TecknoPlay/MQTT-liquid-handler/Pictures/endstop.jpg

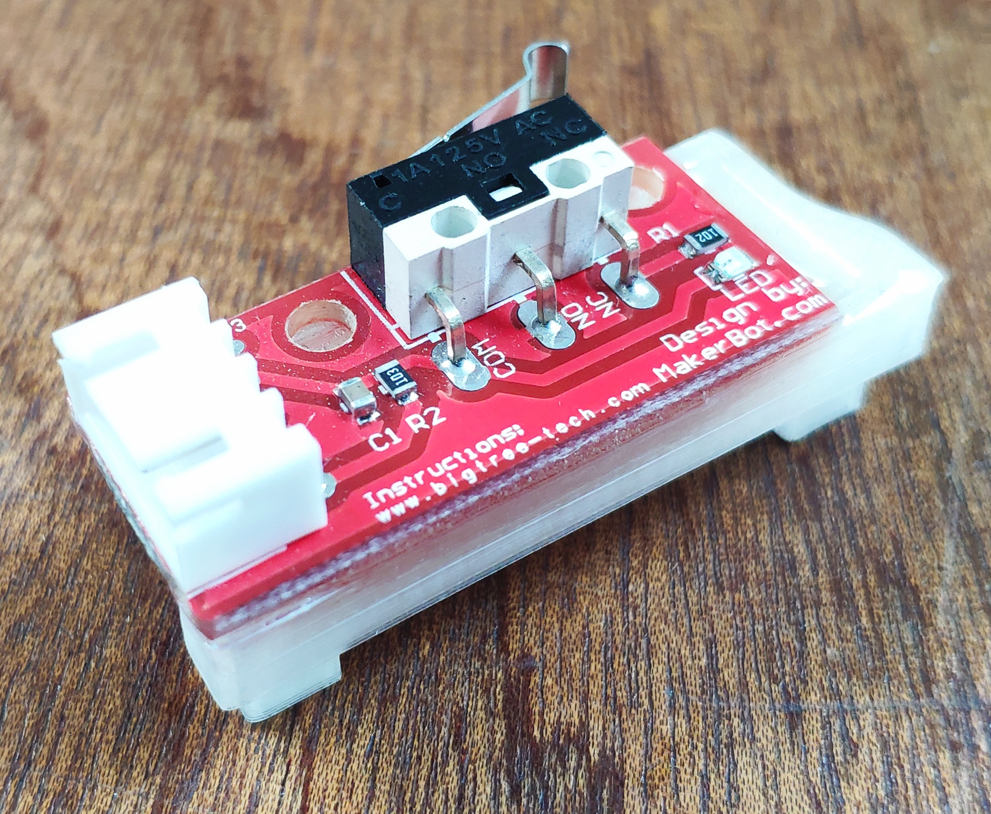
Pictures/endstop.jpg
