TecknoPlay/MQTT-liquid-handler/Pictures/endstop_syr.jpg

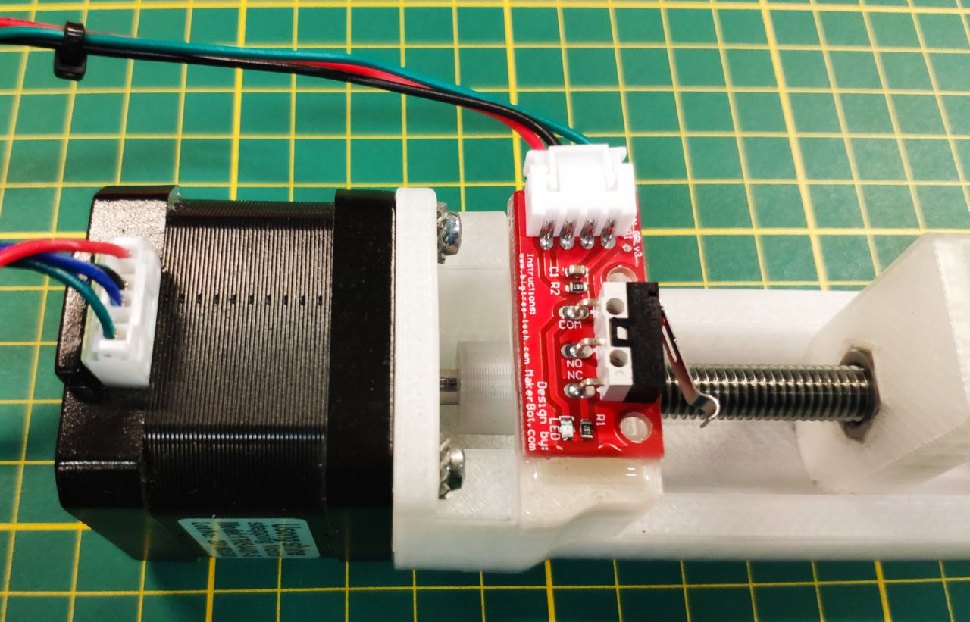
Pictures/endstop_syr.jpg
