TecknoPlay/MQTT-liquid-handler/Pictures/ex_syr.jpg

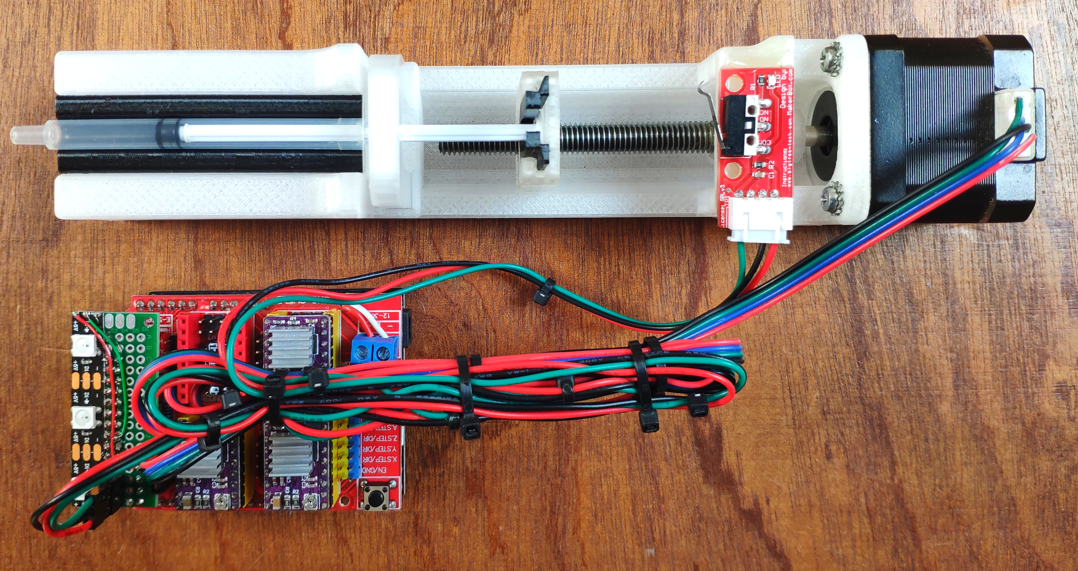
Pictures/ex_syr.jpg
