TecknoPlay/MQTT-liquid-handler/Pictures/modified_shield.jpg

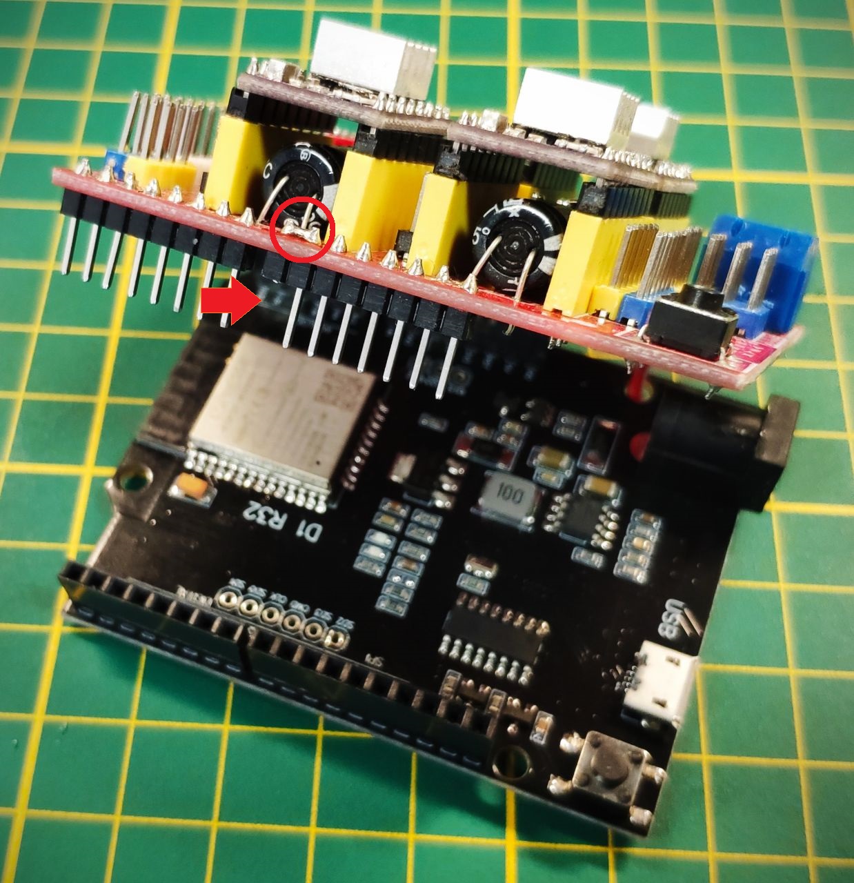
Pictures/modified_shield.jpg
