TecknoPlay/MQTT-liquid-handler/Pictures/pcb_led.jpg

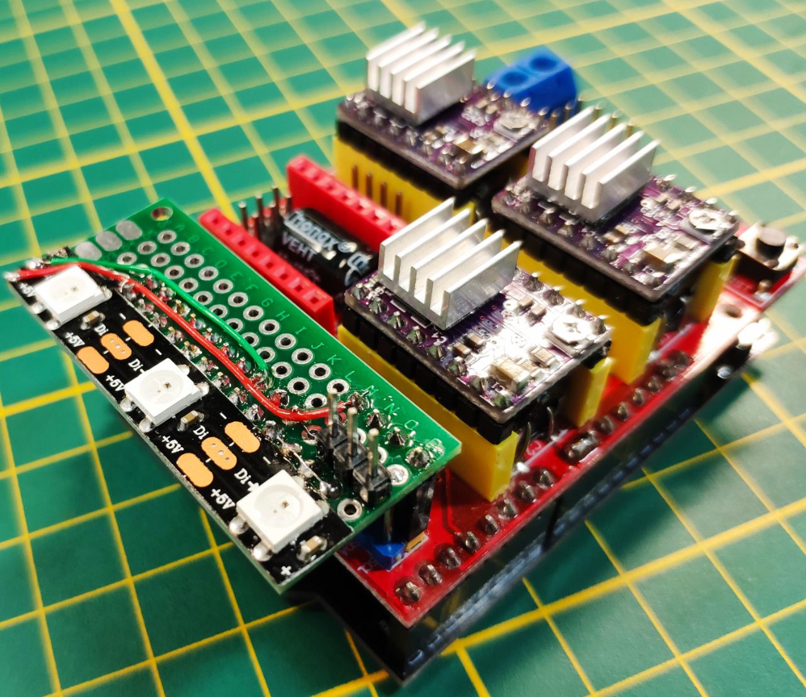
Pictures/pcb_led.jpg
