TecknoPlay/MQTT-liquid-handler/Pictures/rotor_A.jpg

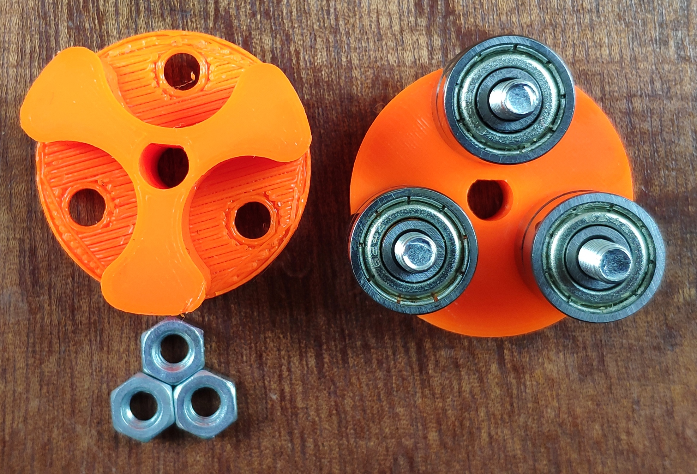
Pictures/rotor_A.jpg
