TecknoPlay/MQTT-liquid-handler/Pictures/stator_A.jpg

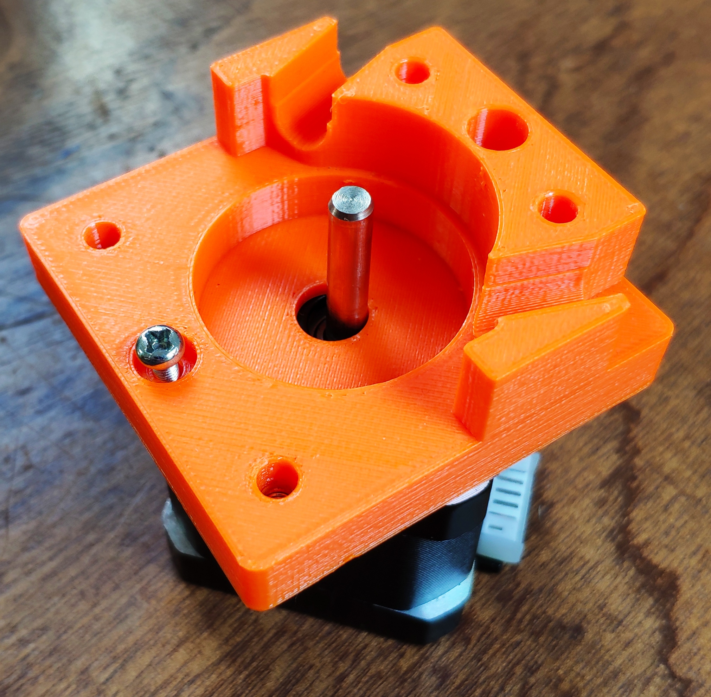
Pictures/stator_A.jpg
