TecknoPlay/MQTT-liquid-handler/Pictures/stator_B.jpg

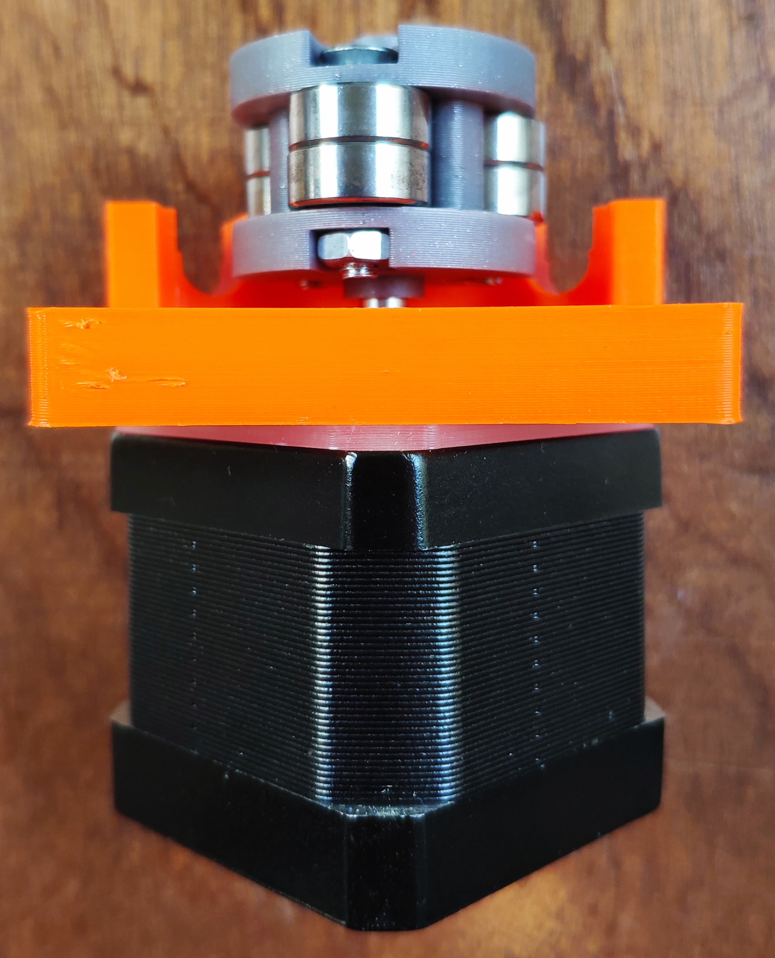
Pictures/stator_B.jpg
