TecknoPlay/MQTT-liquid-handler/Pictures/syr_A.jpg

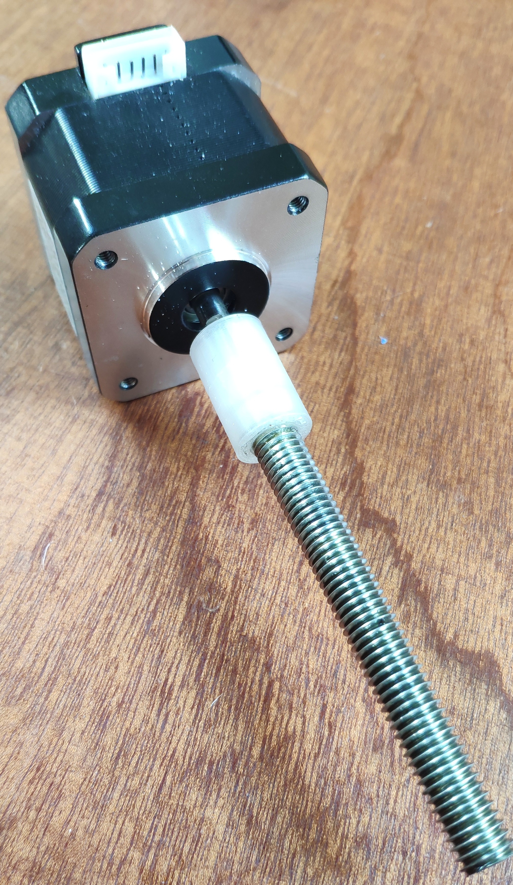
Pictures/syr_A.jpg
