TecknoPlay/MQTT-liquid-handler/Pictures/syr_B.jpg

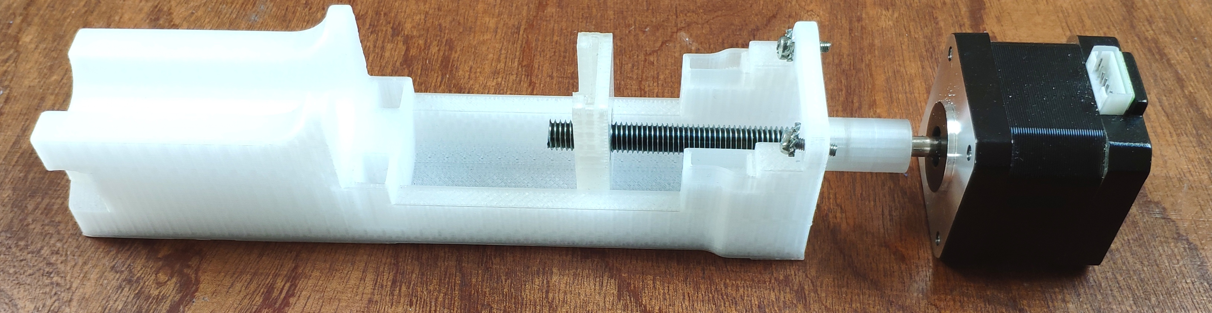
Pictures/syr_B.jpg
