TecknoPlay/MQTT-liquid-handler/Pictures/syr_C.jpg

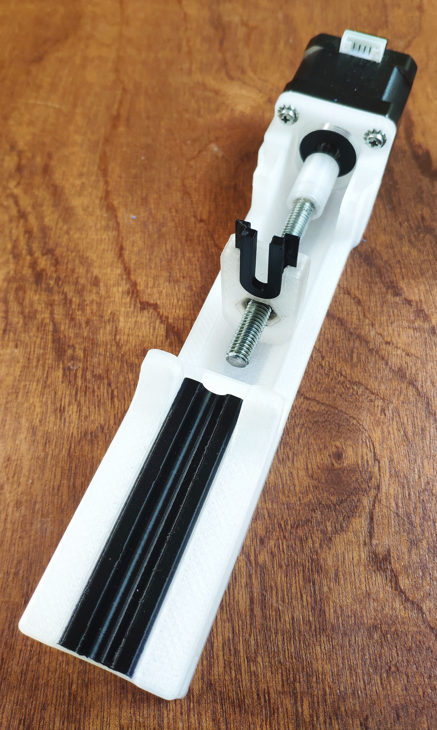
Pictures/syr_C.jpg
