TecknoPlay/MQTT-liquid-handler/Pictures/pump_assembly.jpg

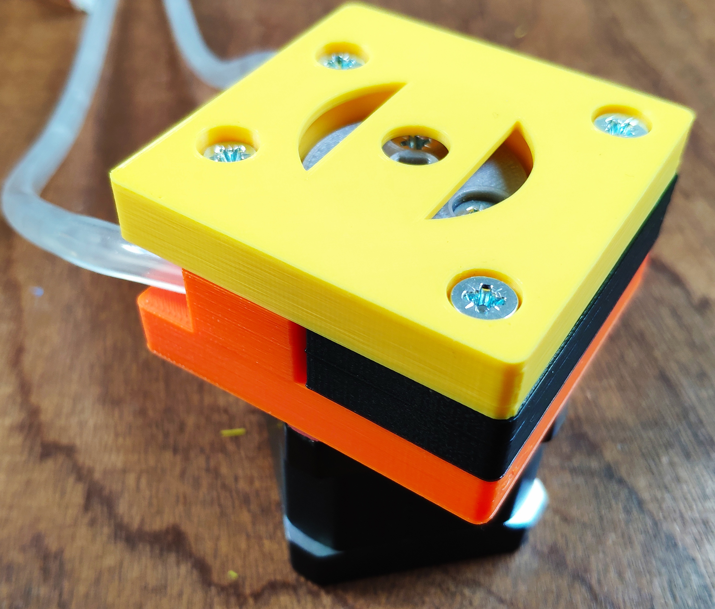
Pictures/pump_assembly.jpg
