TecknoPlay/MQTT-liquid-handler/Pictures/syr_assembly.jpg

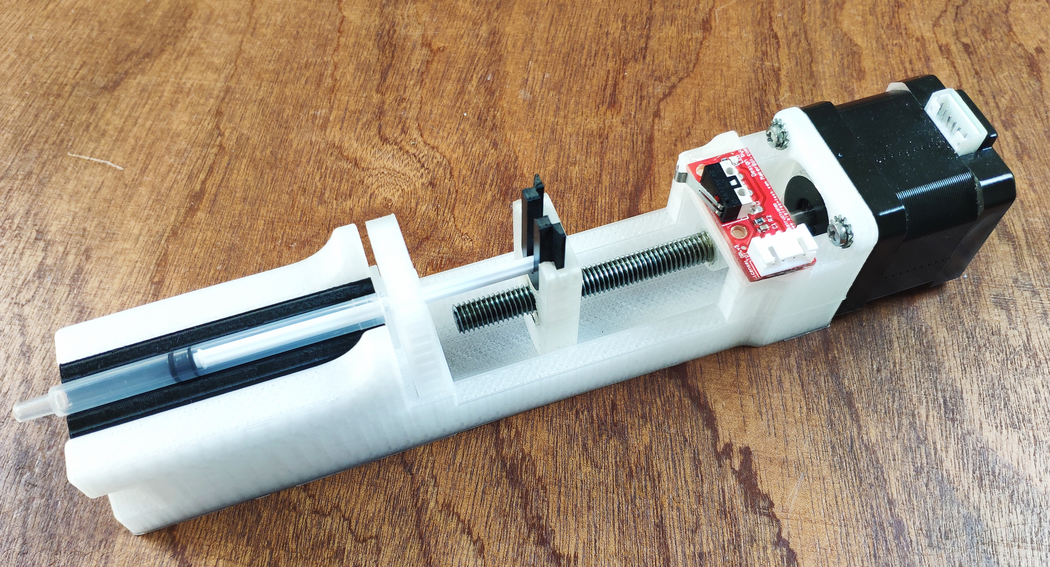
Pictures/syr_assembly.jpg
